p-horrocks/photon-force/src/audio_data.cpp

#include "application.h"

#include "audio_data.h"

namespace audio
{

// Generated from raw file with the command:
// > hexdump -v -e '1/1 "    0x%02x, " 14/1 "0x%02x, " 1/1 " 0x%02x,\n"' ~/Downloads/laser.raw
const uint8_t AUDIO_DATA[] =
{
    0x80, 0x7f, 0x7f, 0x7f, 0x7f, 0x7f, 0x7f, 0x7f, 0x7f, 0x7f, 0x7f, 0x7f, 0x7e, 0x7f, 0x7f, 0x7f,
    0x7f, 0x7f, 0x7e, 0x7f, 0x7f, 0x7f, 0x7f, 0x7f, 0x7f, 0x7f, 0x80, 0x80, 0x80, 0x7f, 0x7f, 0x7f,
    0x80, 0x81, 0x82, 0x82, 0x82, 0x82, 0x82, 0x83, 0x82, 0x80, 0x81, 0x81, 0x84, 0x87, 0x88, 0x84,
    0x7d, 0x7e, 0x84, 0x85, 0x86, 0x85, 0x81, 0x7e, 0x81, 0x83, 0x83, 0x83, 0x82, 0x82, 0x81, 0x83,
    0x85, 0x85, 0x84, 0x80, 0x7f, 0x82, 0x82, 0x82, 0x83, 0x82, 0x82, 0x82, 0x82, 0x82, 0x81, 0x81,
    0x83, 0x85, 0x84, 0x80, 0x7e, 0x7f, 0x82, 0x85, 0x86, 0x83, 0x7d, 0x7b, 0x7c, 0x80, 0x81, 0x83,
    0x82, 0x7c, 0x78, 0x7b, 0x7e, 0x81, 0x81, 0x7c, 0x78, 0x77, 0x7b, 0x7e, 0x80, 0x81, 0x7f, 0x7a,
    0x77, 0x77, 0x79, 0x7b, 0x7d, 0x7d, 0x7a, 0x78, 0x78, 0x7a, 0x7c, 0x7d, 0x7d, 0x79, 0x75, 0x76,
    0x78, 0x7c, 0x80, 0x81, 0x7d, 0x76, 0x75, 0x78, 0x79, 0x7a, 0x7c, 0x7d, 0x7b, 0x7a, 0x7a, 0x7d,
    0x80, 0x81, 0x81, 0x7e, 0x7d, 0x7f, 0x81, 0x83, 0x81, 0x7d, 0x7b, 0x7b, 0x7d, 0x80, 0x82, 0x81,
    0x7e, 0x7b, 0x7e, 0x82, 0x83, 0x85, 0x80, 0x7f, 0x80, 0x84, 0x8a, 0x8e, 0x8d, 0x84, 0x7e, 0x7b,
    0x81, 0x87, 0x85, 0x82, 0x7c, 0x81, 0x7e, 0x83, 0x88, 0x85, 0x87, 0x77, 0x7d, 0x7d, 0x7f, 0x8d,
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
    0xa5, 0x92, 0x76, 0x68, 0x65, 0x77, 0x98, 0xa4, 0x8b, 0x73, 0x5e, 0x55, 0x61, 0x65, 0x7f, 0x90,
    0x6c, 0x4f, 0x59, 0x63, 0x62, 0x77, 0x99, 0x91, 0x73, 0x63, 0x5c, 0x67, 0x77, 0x94, 0xa5, 0x91,
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
};

const uint32_t AUDIO_DATA_SIZE = sizeof(AUDIO_DATA);

} // namespace audio
